antarcticlion/RGB_UNICONV/images/DE9_98XL_A.png

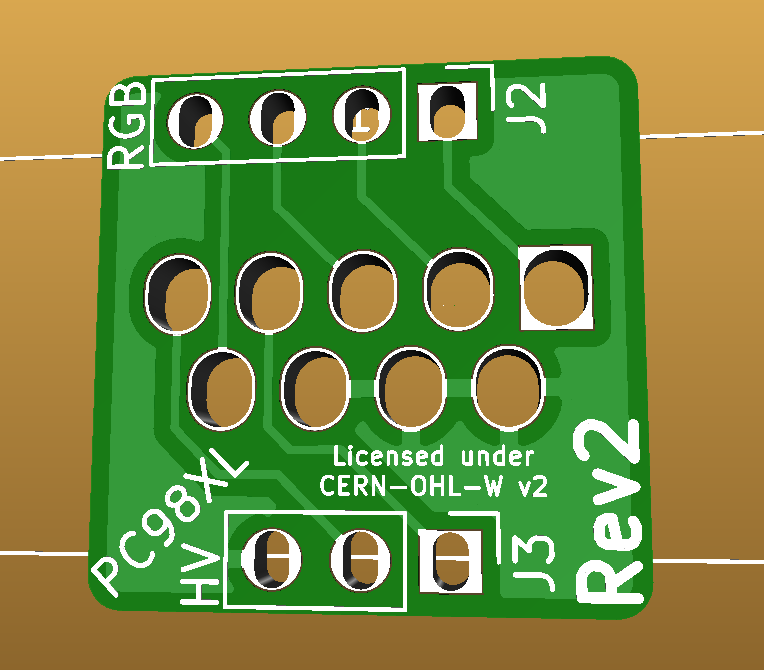
images/DE9_98XL_A.png
