antarcticlion/RGB_UNICONV/images/DE9_98XL_B.png

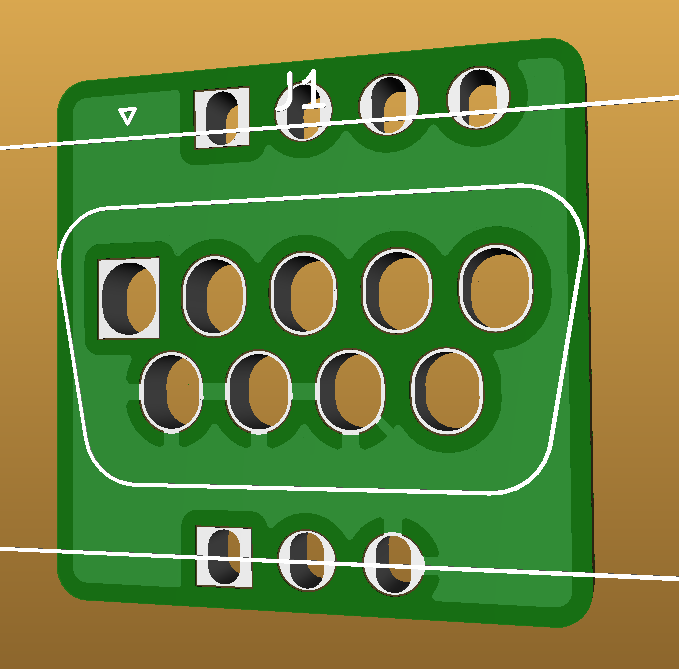
images/DE9_98XL_B.png
