antarcticlion/RGB_UNICONV/images/image003.jpg

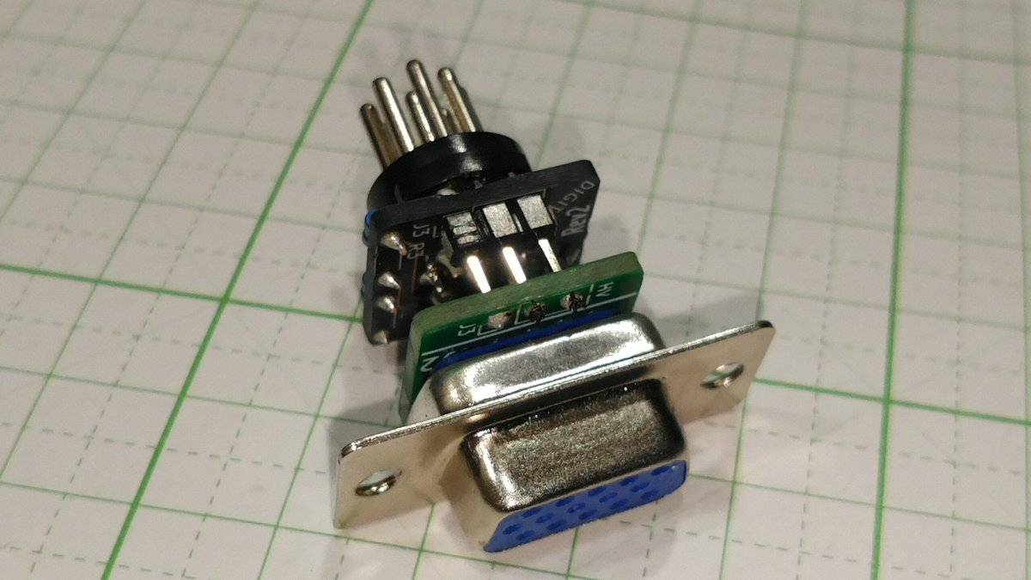
images/image003.jpg
