antarcticlion/RGB_UNICONV/images/making003.JPG

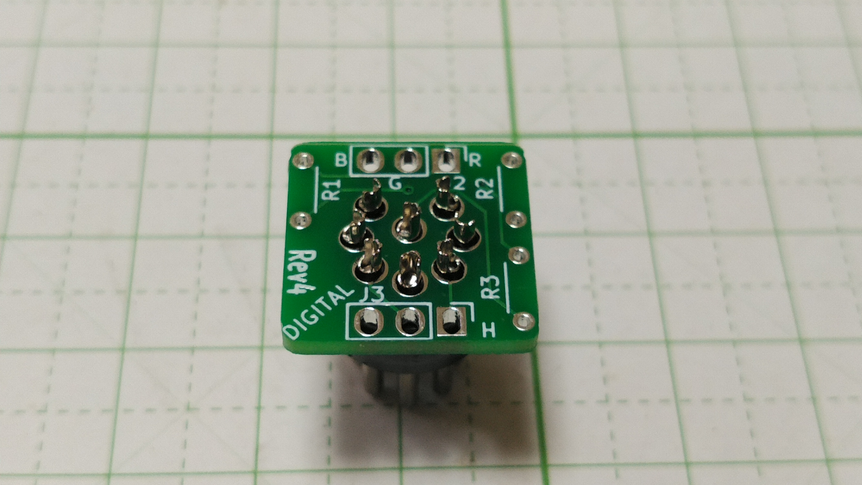
images/making003.JPG
