antarcticlion/RGB_UNICONV/images/making004.JPG

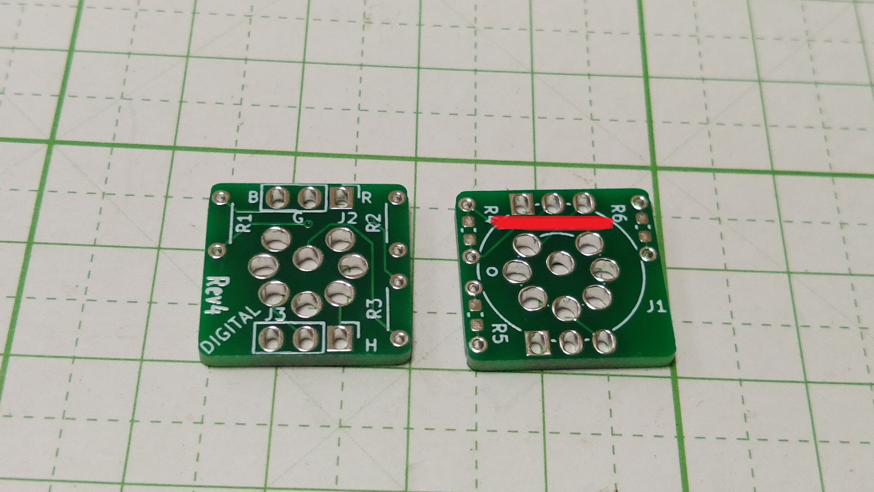
images/making004.JPG
