antarcticlion/RGB_UNICONV/images/making005.JPG

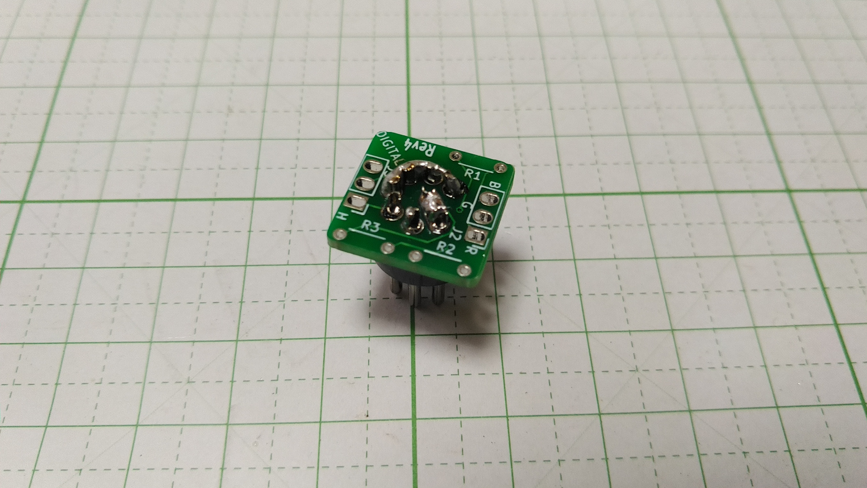
images/making005.JPG
