antarcticlion/RGB_UNICONV/images/making008.JPG

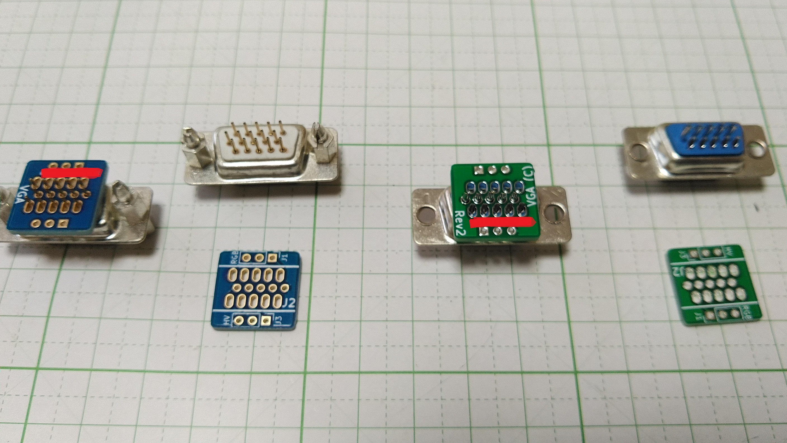
images/making008.JPG
