antarcticlion/RGB_UNICONV/images/making009.JPG

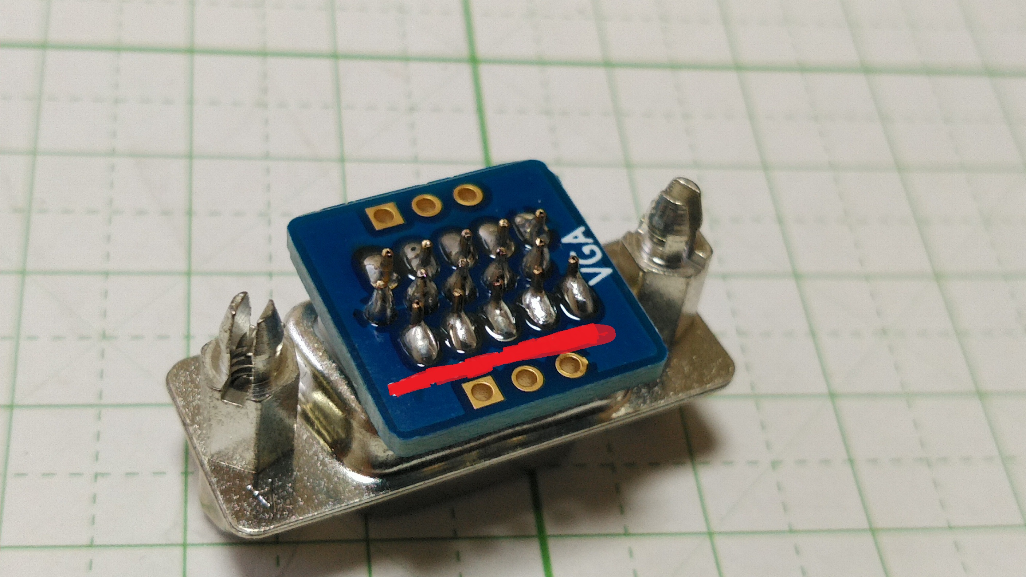
images/making009.JPG
