antarcticlion/RGB_UNICONV/images/making010.JPG

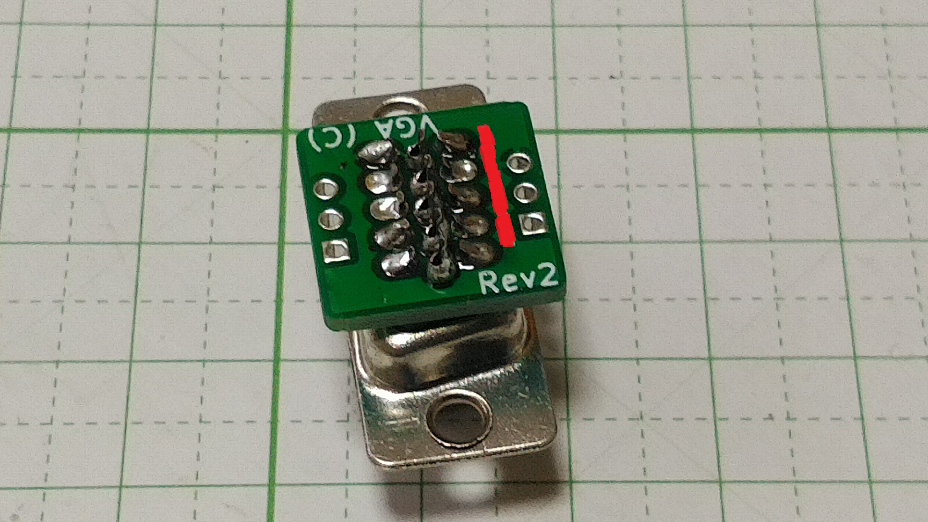
images/making010.JPG
