antarcticlion/RGB_UNICONV/images/making012.JPG

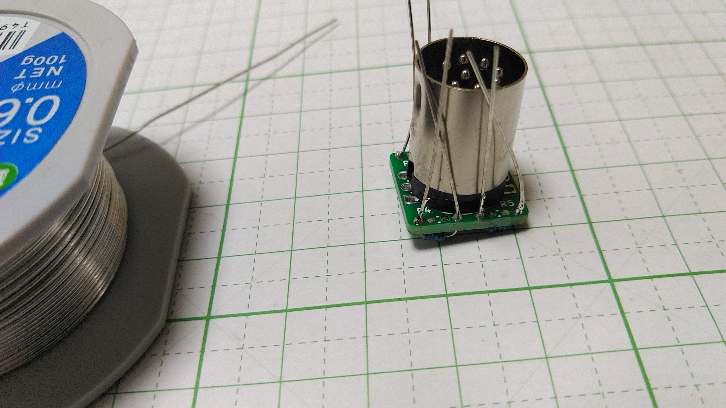
images/making012.JPG
