antarcticlion/RGB_UNICONV/images/making015.JPG

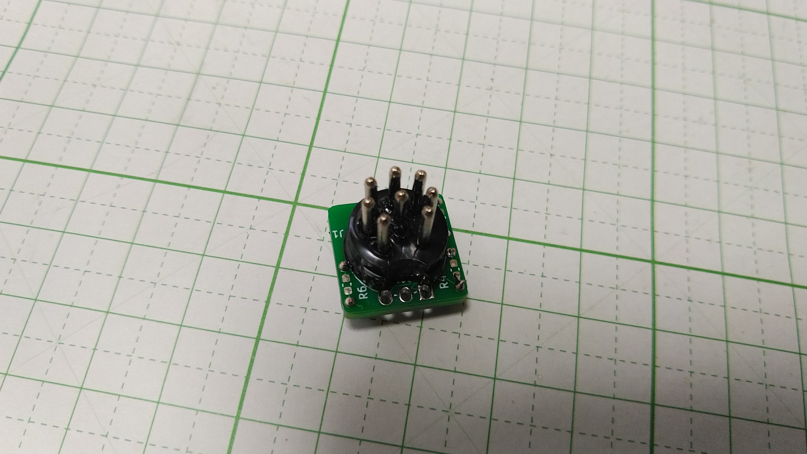
images/making015.JPG
