antarcticlion/RGB_UNICONV/images/making016.JPG

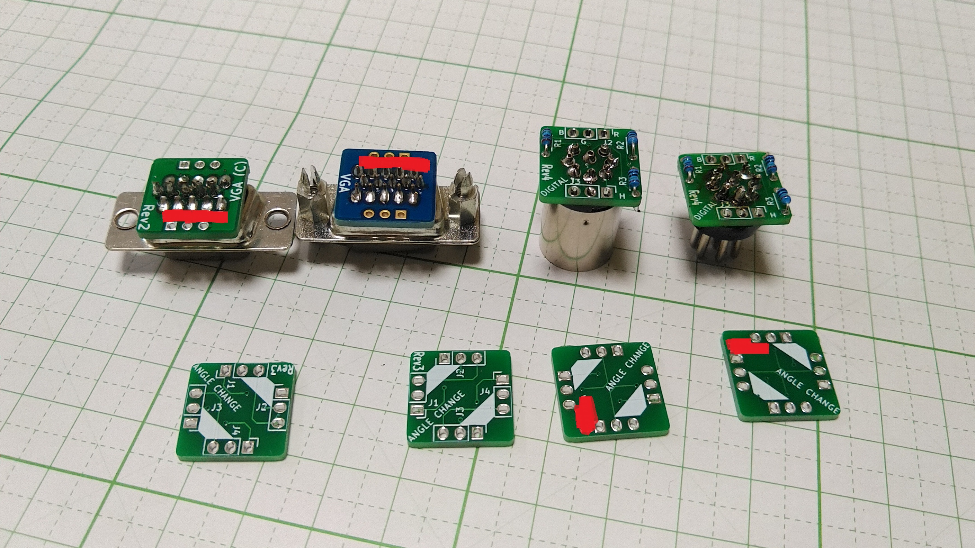
images/making016.JPG
