antarcticlion/RGB_UNICONV/images/making017.JPG

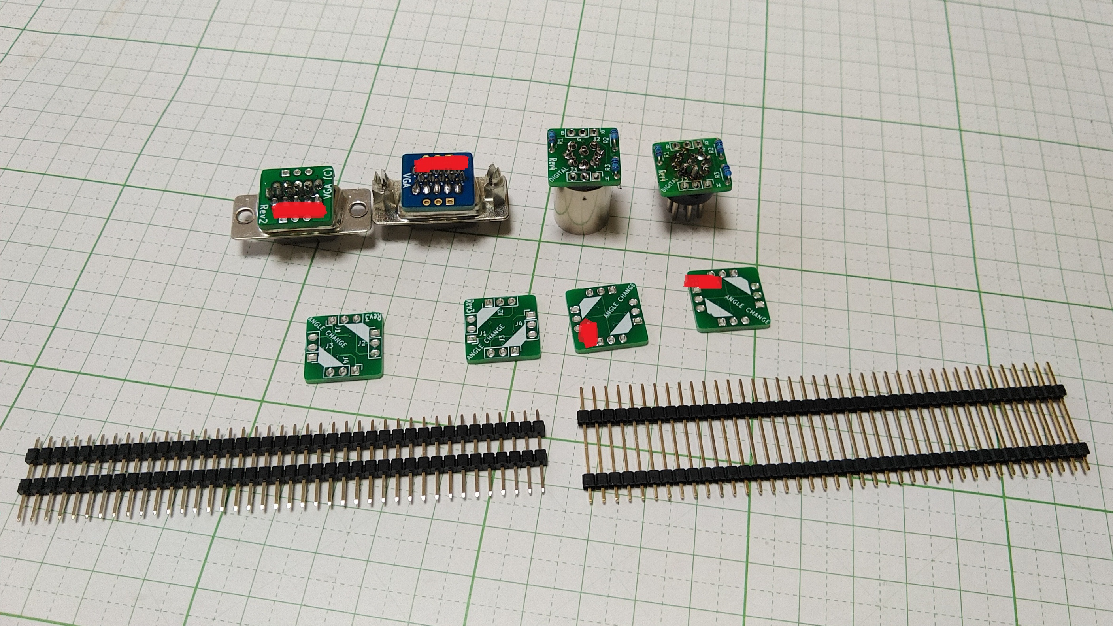
images/making017.JPG
