antarcticlion/RGB_UNICONV/images/making019.JPG

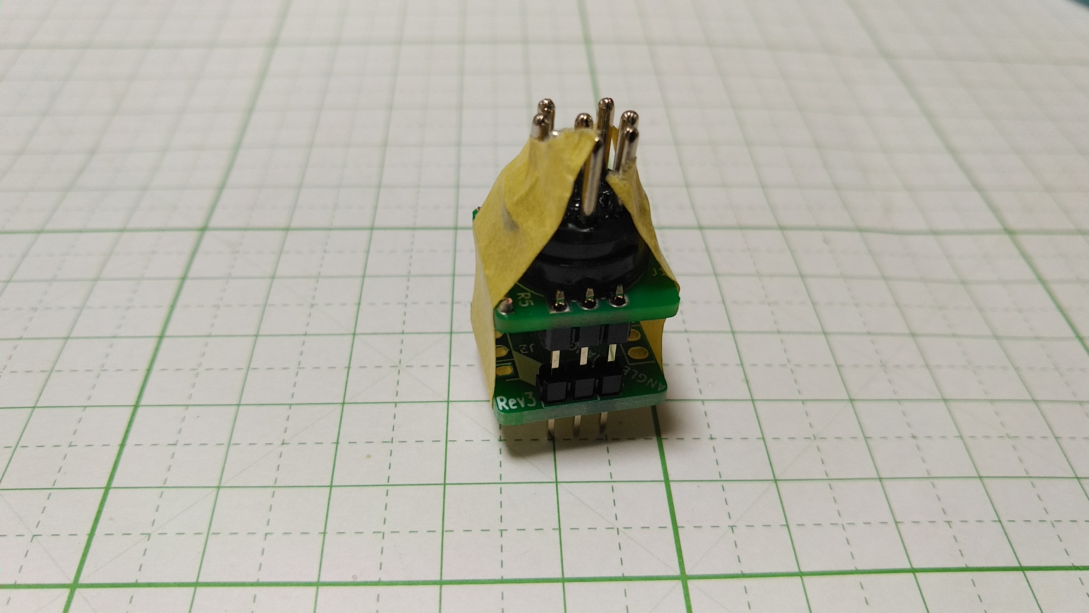
images/making019.JPG
