antarcticlion/RGB_UNICONV/images/making020.JPG

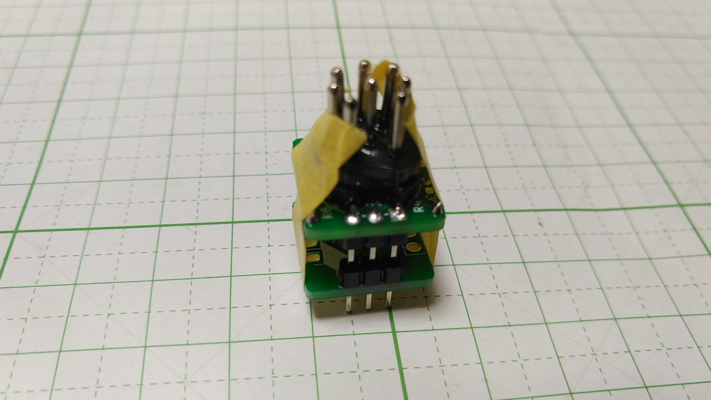
images/making020.JPG
