antarcticlion/RGB_UNICONV/images/making021.JPG

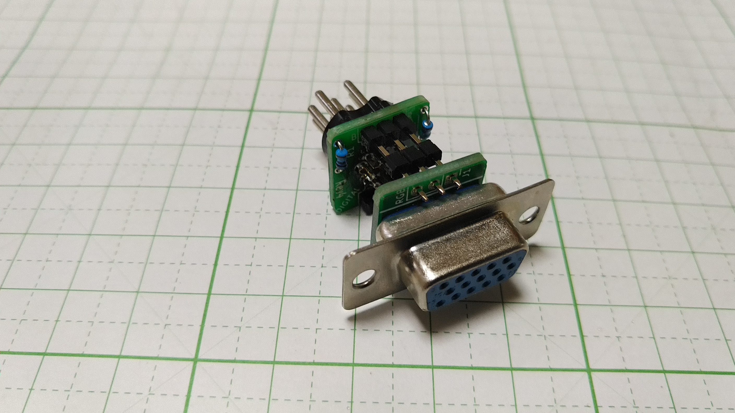
images/making021.JPG
