antarcticlion/RGB_UNICONV/images/making022.JPG

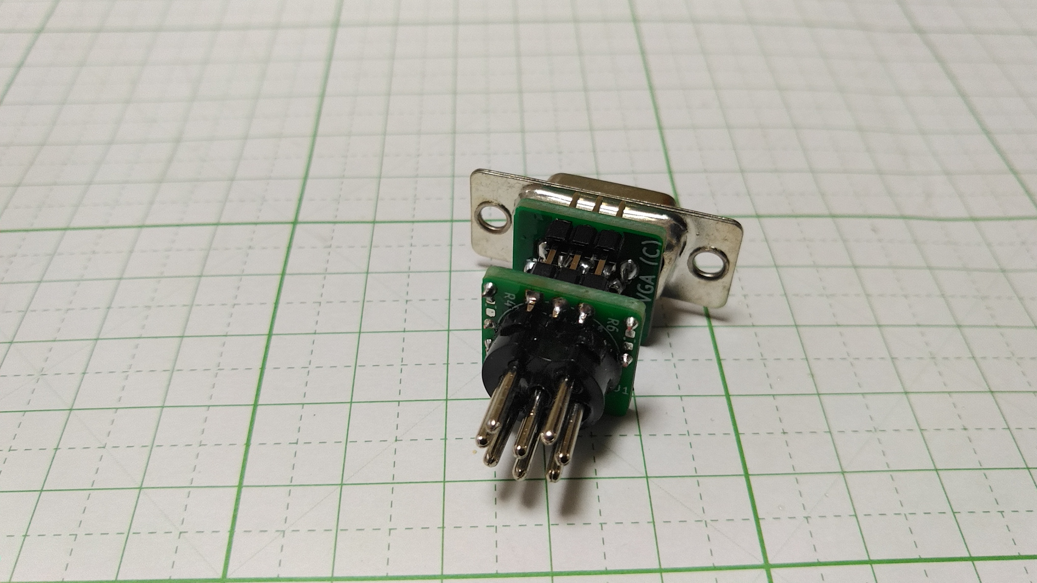
images/making022.JPG
