antarcticlion/RGB_UNICONV/images/making023.JPG

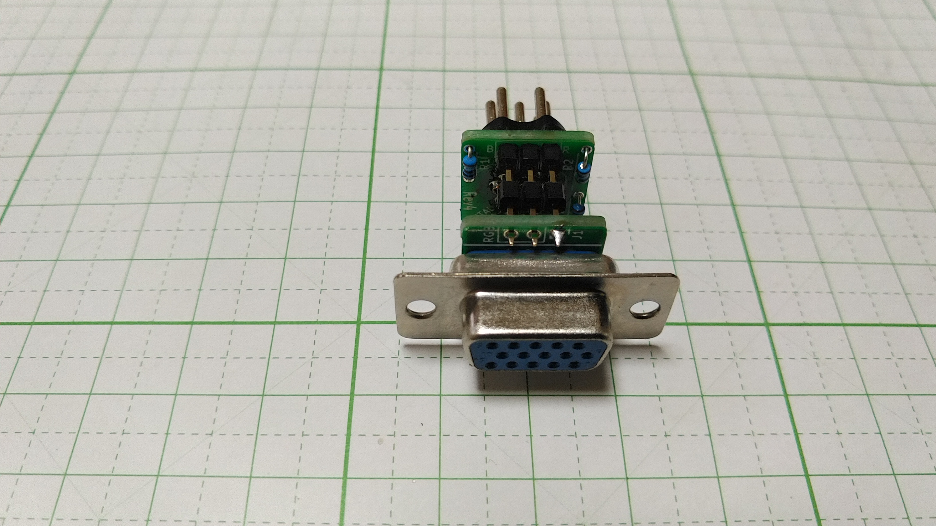
images/making023.JPG
