antarcticlion/RGB_UNICONV/images/making024.JPG

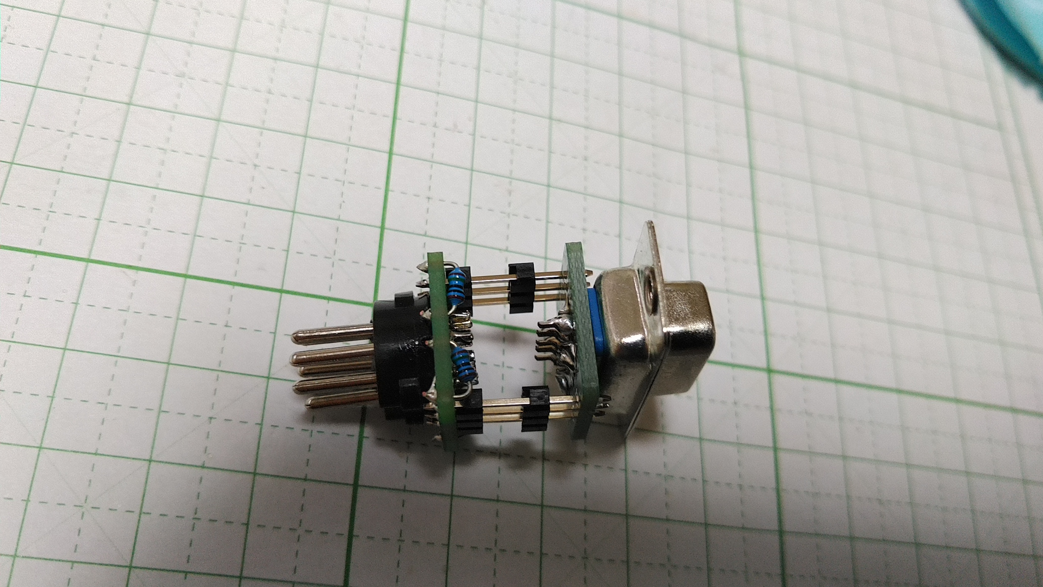
images/making024.JPG
