antarcticlion/RGB_UNICONV/images/making025.JPG

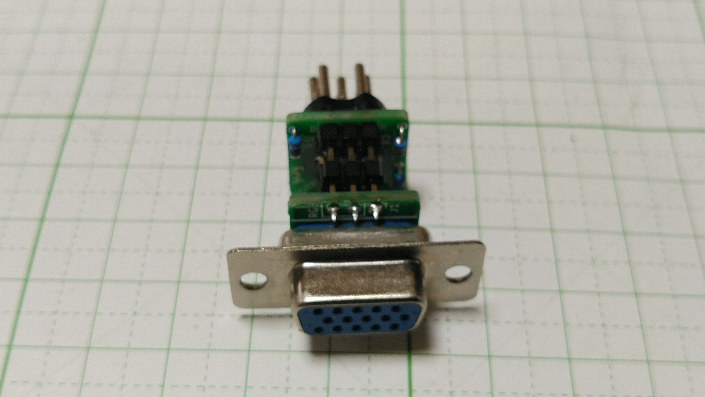
images/making025.JPG
