antarcticlion/RGB_UNICONV/images/making026.JPG

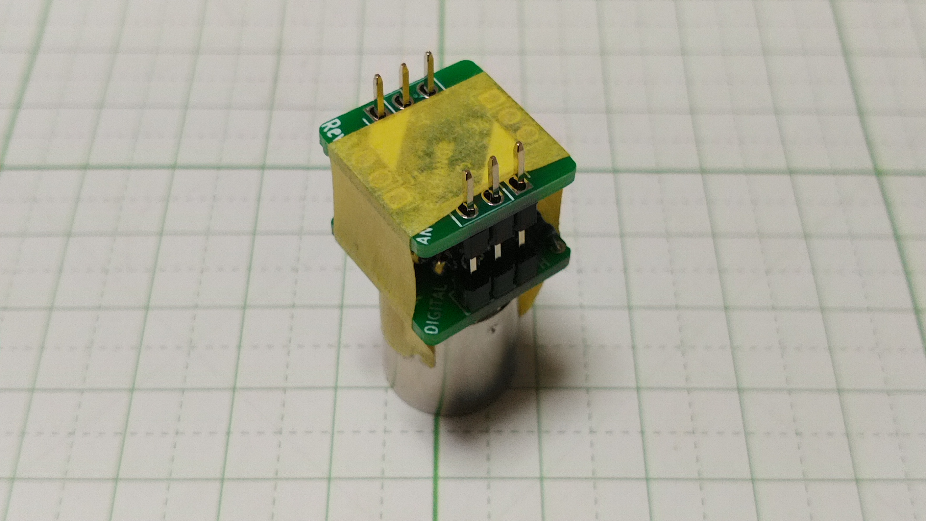
images/making026.JPG
