antarcticlion/RGB_UNICONV/images/making029.JPG

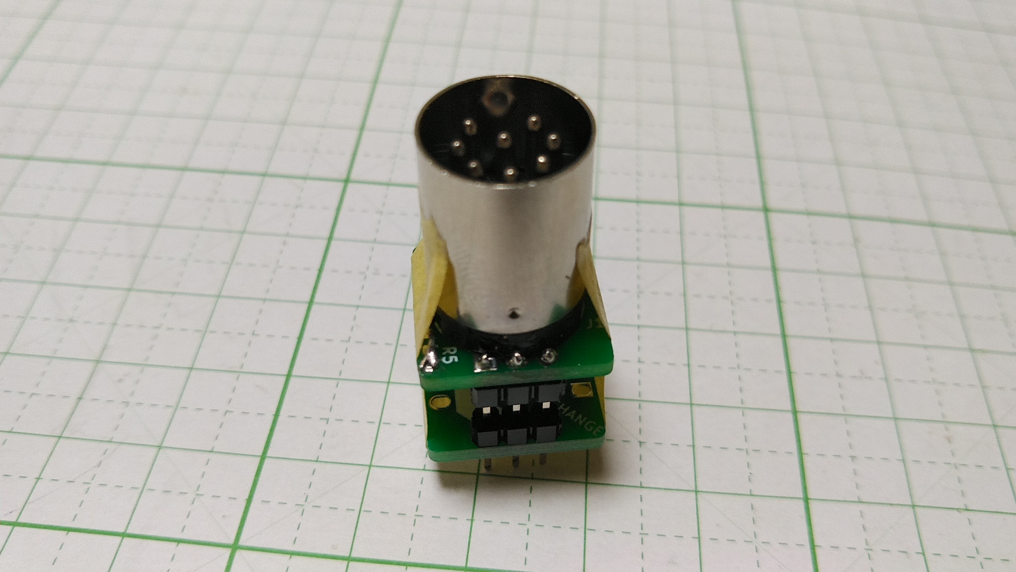
images/making029.JPG
