antarcticlion/RGB_UNICONV/images/making031.JPG

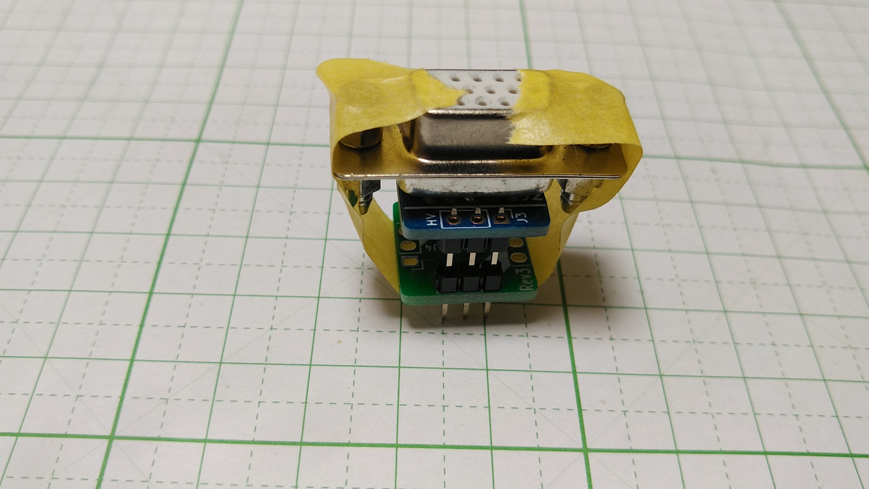
images/making031.JPG
