antarcticlion/RGB_UNICONV/images/making032.JPG

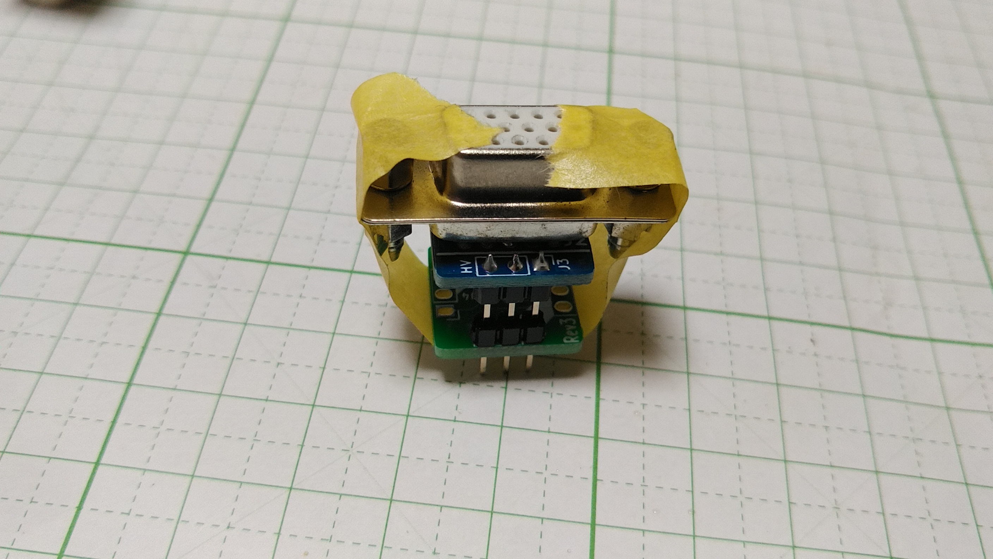
images/making032.JPG
