antarcticlion/RGB_UNICONV/images/making033.JPG

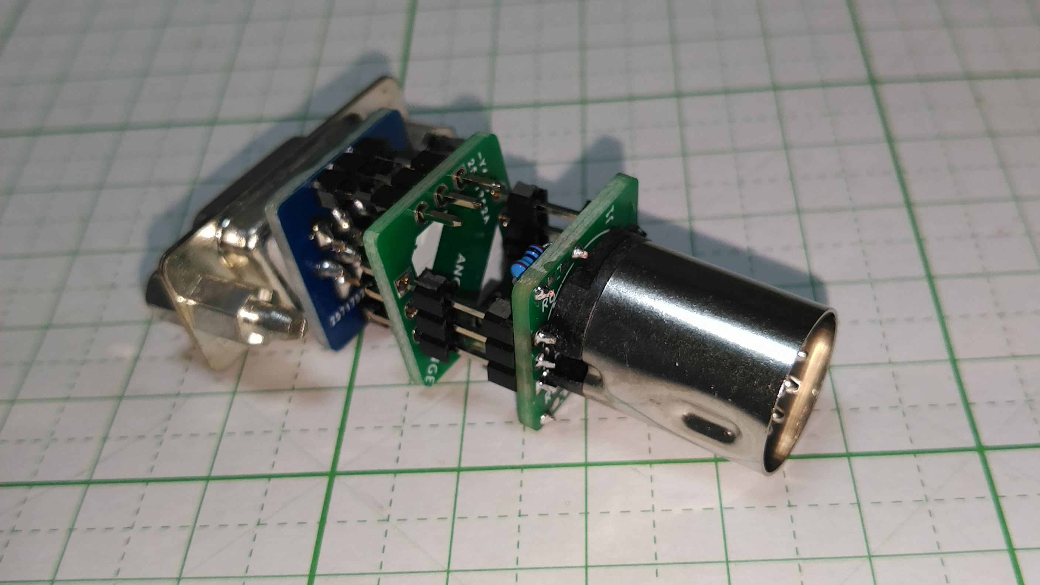
images/making033.JPG
