antarcticlion/RGB_UNICONV/images/making034.JPG

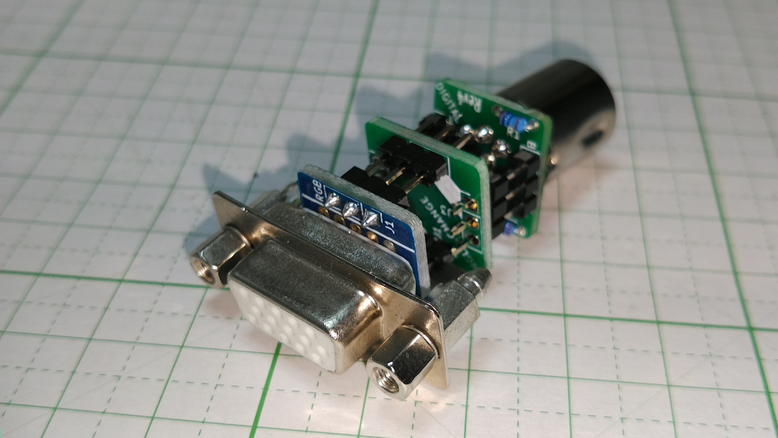
images/making034.JPG
