antarcticlion/RGB_UNICONV/images/making035.JPG

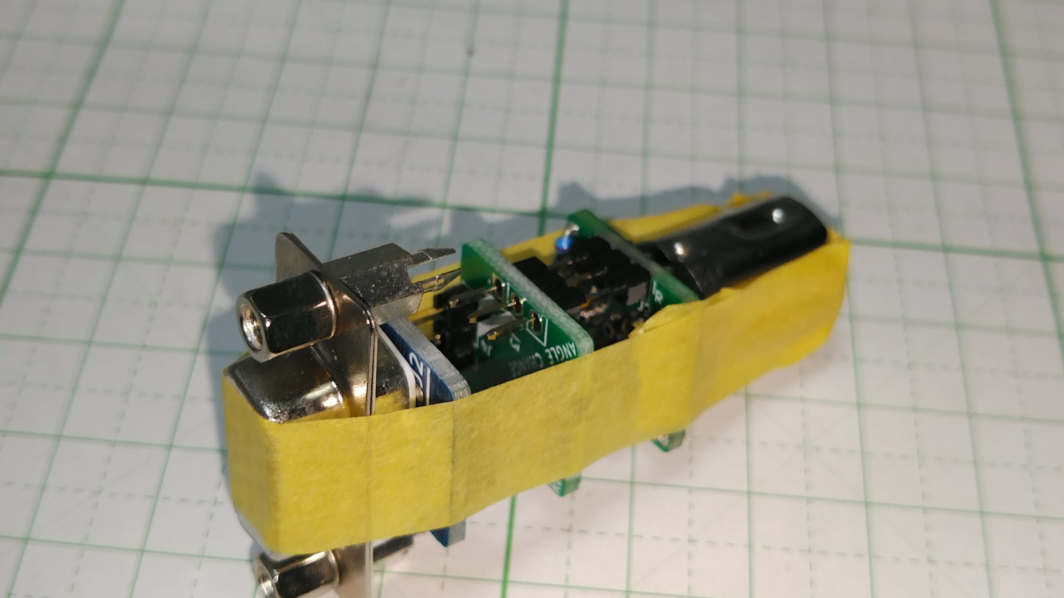
images/making035.JPG
