antarcticlion/RGB_UNICONV/images/making036.JPG

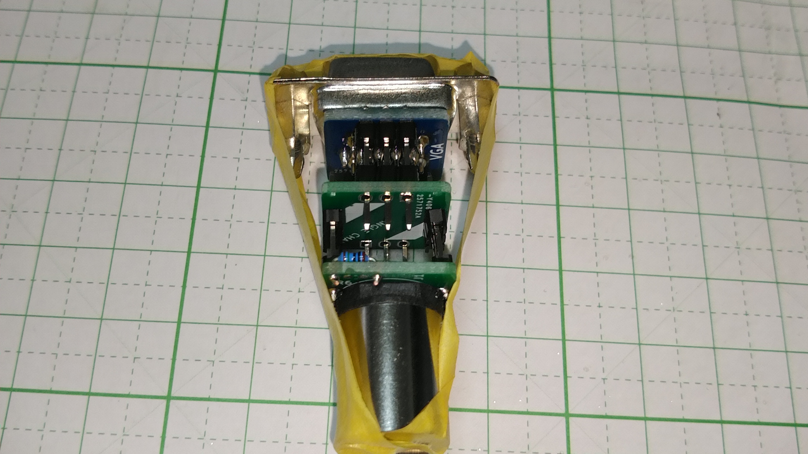
images/making036.JPG
