antarcticlion/RGB_UNICONV/images/making037.JPG

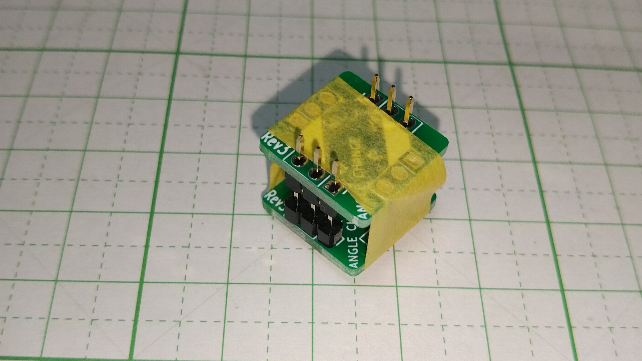
images/making037.JPG
