antarcticlion/RGB_UNICONV/images/making038.JPG

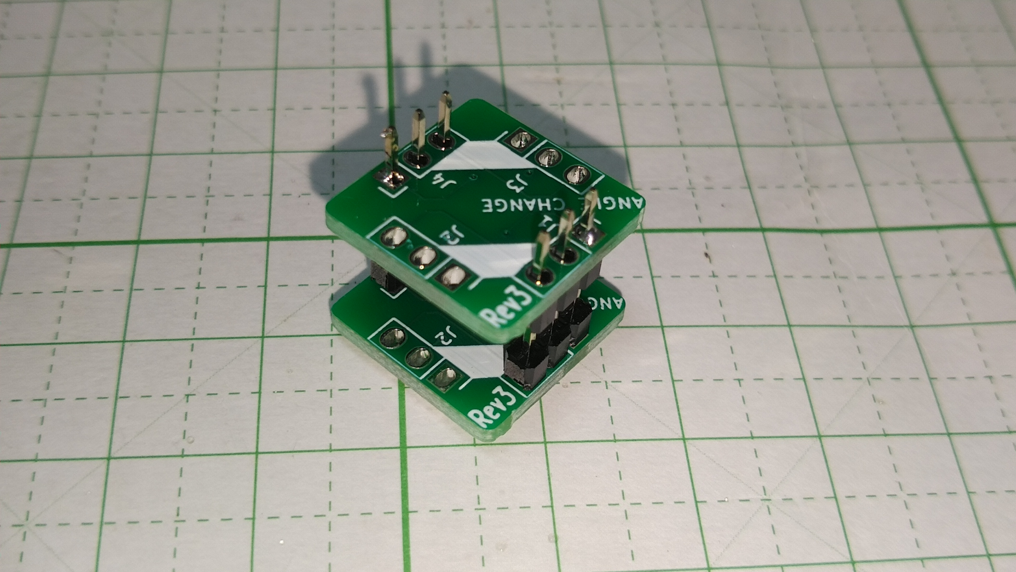
images/making038.JPG
