antarcticlion/RGB_UNICONV/images/making039.JPG

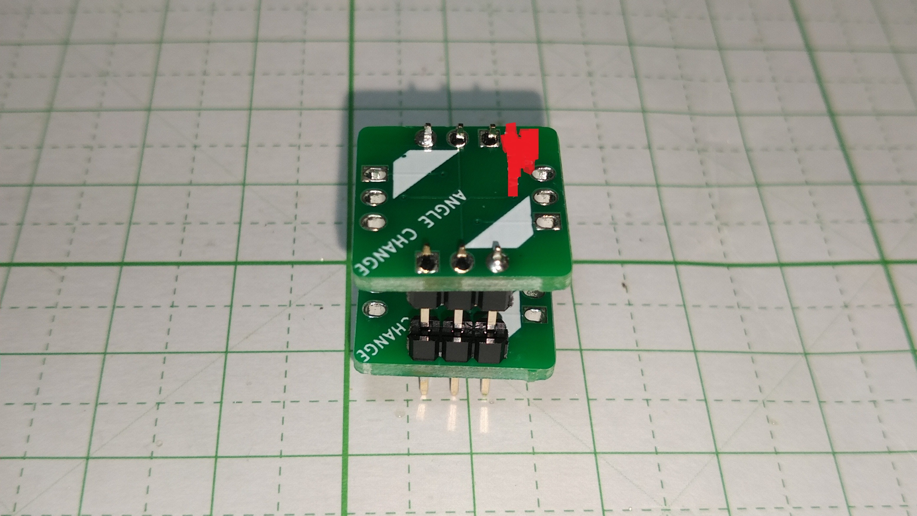
images/making039.JPG
