antarcticlion/RGB_UNICONV/images/making040.JPG

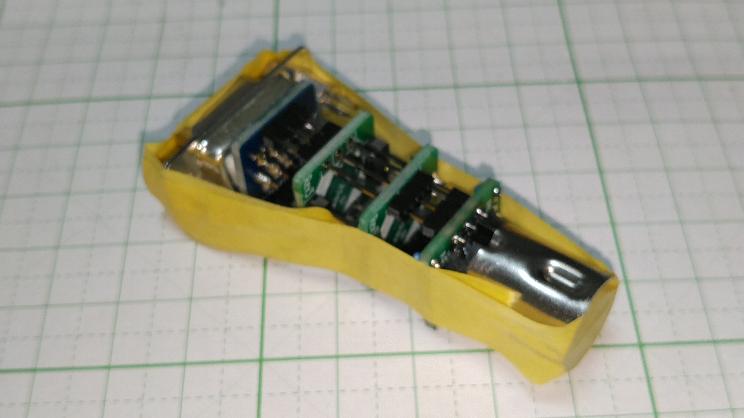
images/making040.JPG
