antarcticlion/RGB_UNICONV/images/making041.JPG

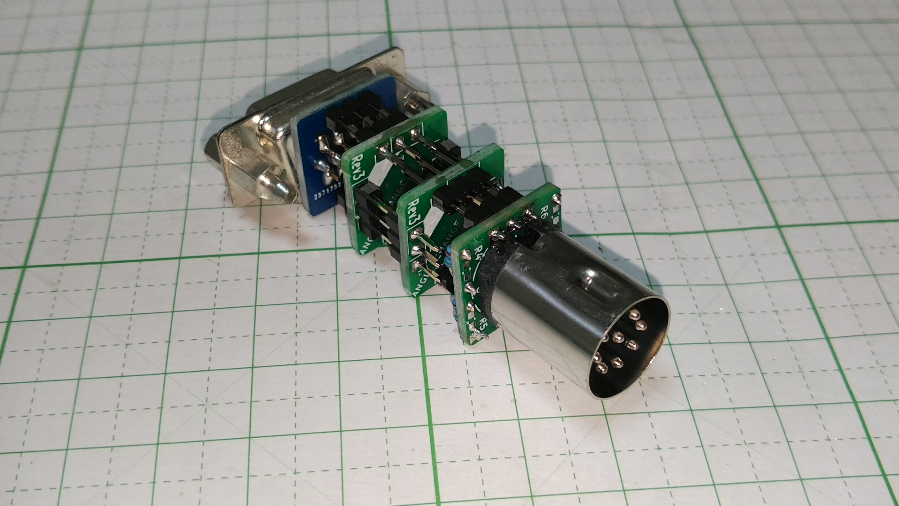
images/making041.JPG
