antarcticlion/RGB_UNICONV/images/making042.JPG

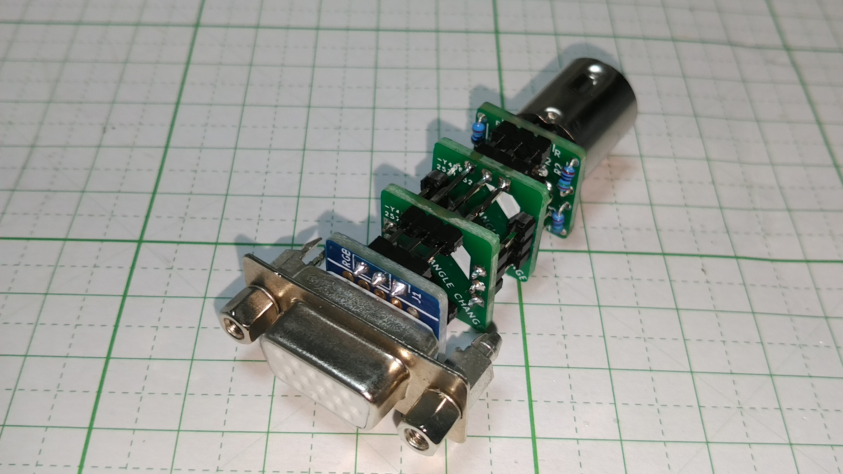
images/making042.JPG
