antarcticlion/RGB_UNICONV/images/making043.JPG

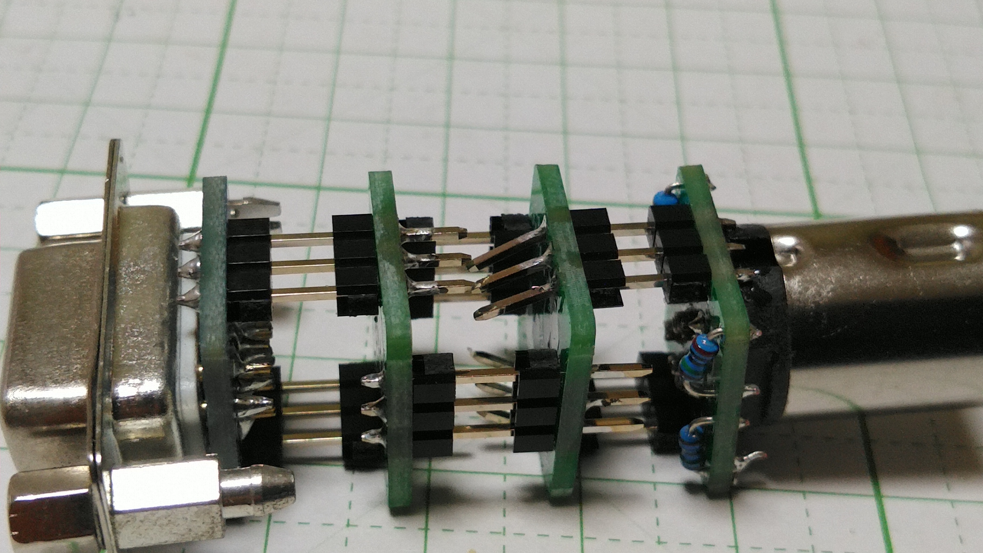
images/making043.JPG
