antarcticlion/RGB_UNICONV/images/making044.JPG

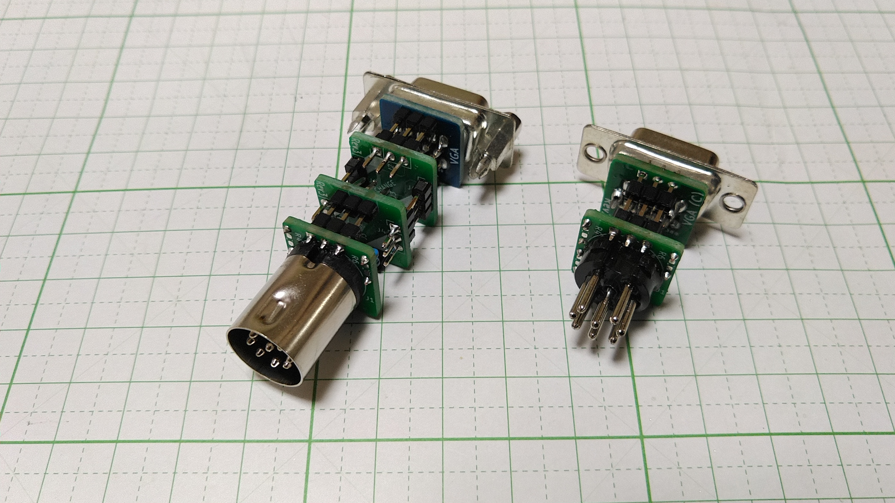
images/making044.JPG
